robs-tech-workbench/hexapod_spiderbot_tutorials/media/youtube_tuts.png

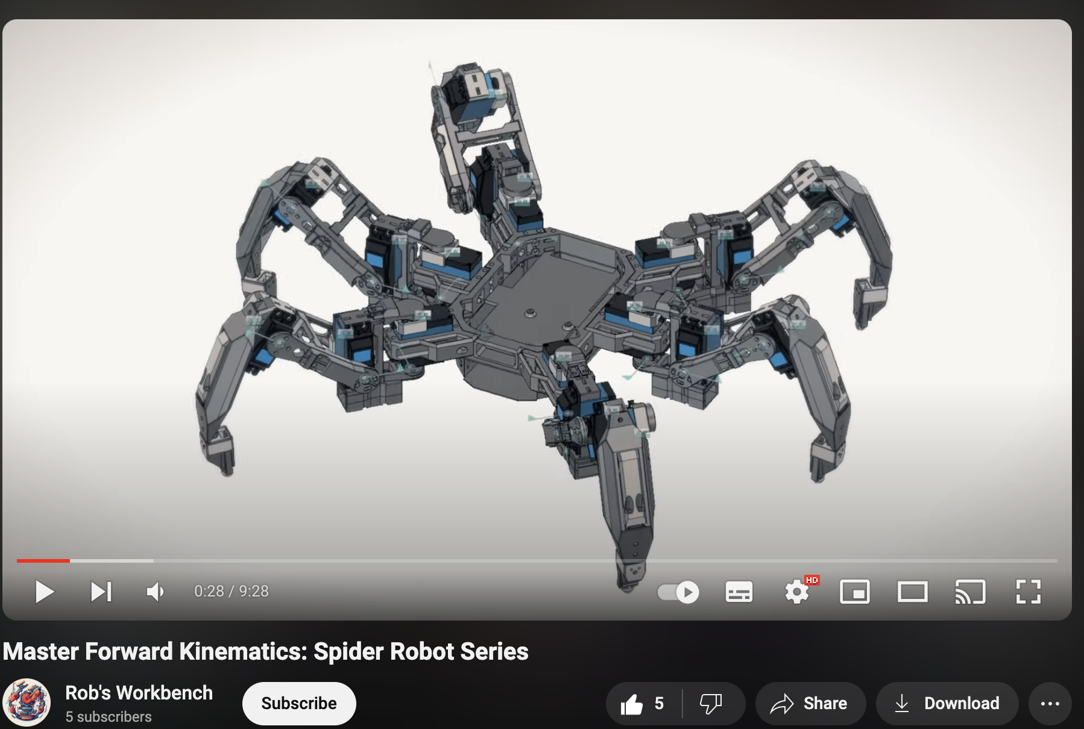
media/youtube_tuts.png
