robs-tech-workbench/hexapod_spiderbot_tutorials/tutorial_tools_hardware_3d_parts_spider_robot/media/51rFqlV6QrL.jpg

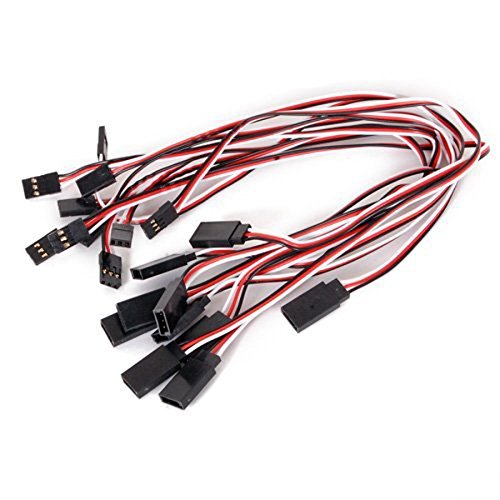
tutorial_tools_hardware_3d_parts_spider_robot/media/51rFqlV6QrL.jpg
