robs-tech-workbench/hexapod_spiderbot_tutorials/tutorial_tools_hardware_3d_parts_spider_robot/media/s-l1600.jpg

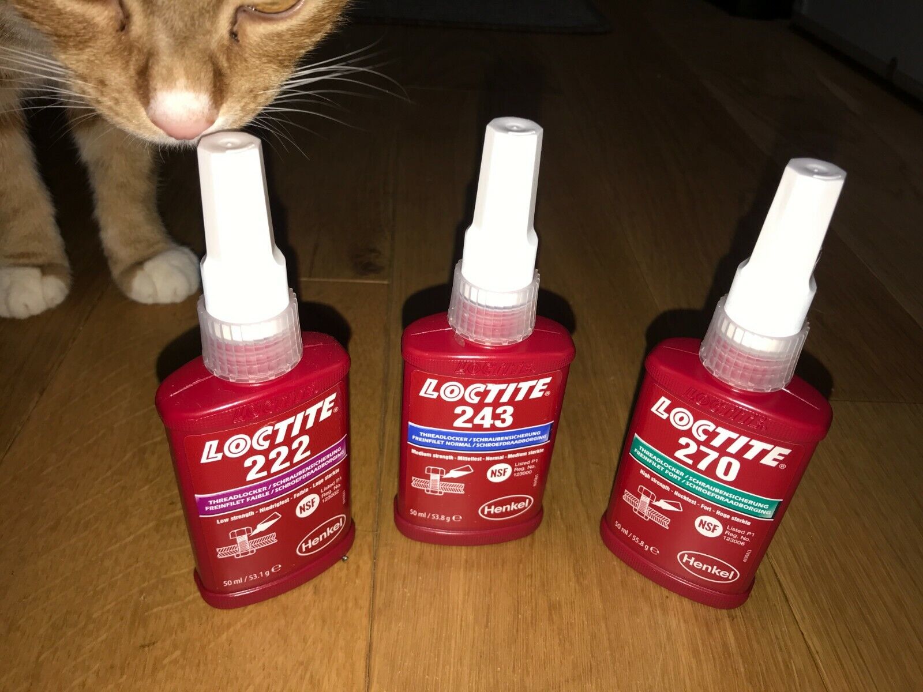
tutorial_tools_hardware_3d_parts_spider_robot/media/s-l1600.jpg
