robs-tech-workbench/hexapod_spiderbot_tutorials/tutorial_tools_hardware_3d_parts_spider_robot/media/servo-2040-1_768x768.webp

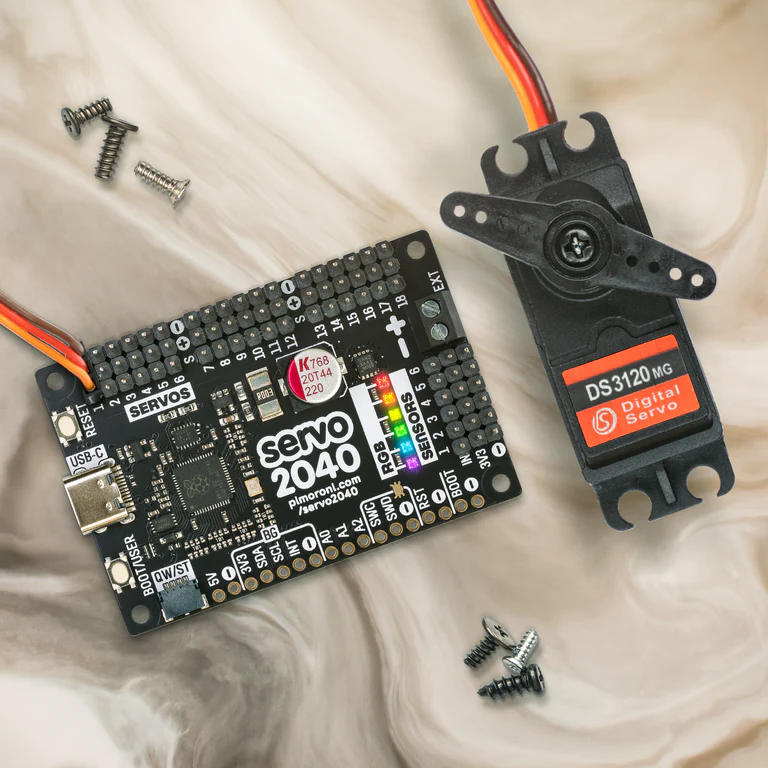
tutorial_tools_hardware_3d_parts_spider_robot/media/servo-2040-1_768x768.webp
