robs-tech-workbench/hexapod_spiderbot_tutorials/tutorial_controll_one_leg/last_commenter_thumbnail.jpg

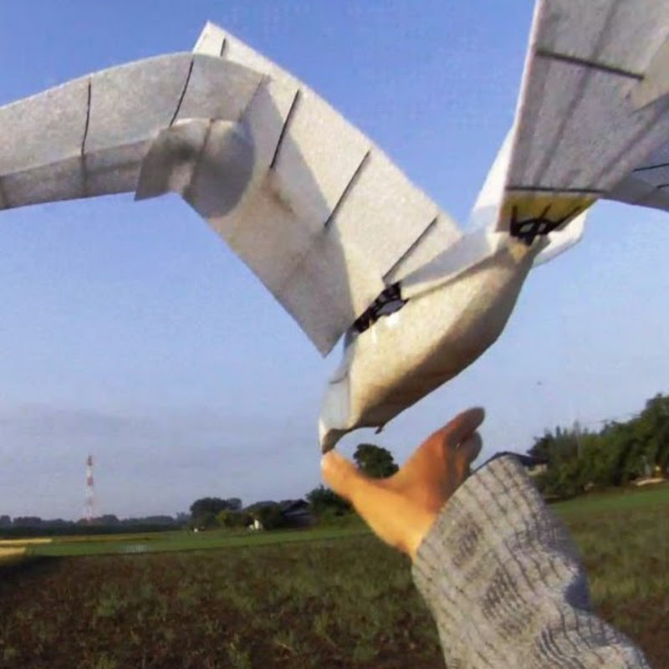
tutorial_controll_one_leg/last_commenter_thumbnail.jpg
